shimniok/lma/firmware/morse.h

#ifndef __MORSE_H
#define __MORSE_H

// times in ms
#define DOT       60
#define DASH      DOT*3
#define SPACE     DOT    // intra character space
#define WORDSPACE DOT*7  // intra word space

#define OK "--- -.-"
#define SOS "... --- ..."
#define WARNING ".--"
#define CONFIG "-.-."

void dit();
void dah();
void space();
void message(char *m);
void fives(int n);
void number(uint8_t n);

#endif
