shimniok/lma/firmware/switch.c

#include "config.h"
#include "switch.h"

#define pressed() ((PINB & _BV(SWITCH)) == 0);

void init_switch(void)
{
  // initialize ISR

  // Set switch as input
  DDRB &= ~_BV(SWITCH);

  // Set pullup on switch
  PORTB |= _BV(SWITCH);
}

bool switch_pressed(void)
{
  bool result = 0;

  result = pressed();
  _delay_ms(50); // debounce

  return result & pressed();
}
